gratinDeTopinambour/Reflow_Soldering_DIY/Code_stm32/Drivers/OLED_096/Src/pixel_font.c

/*
 * pixel_font.c
 *
 *  Created on: Oct 25, 2025
 *      Author: valentin
 */

#include "pixel_font.h"

const uint8_t bpixel [] =
{
	// Character: '0'
	0b11000001,
	0b10111010,
	0b10110110,
	0b10101110,
	0b11000001,

	// Character: '1'
	0b11111111,
	0b10111101,
	0b10000000,
	0b10111111,
	0b11111111,

	//Character: 2
	0b10111101,
	0b10011110,
	0b10101110,
	0b10110110,
	0b10111001,

	//Character: 3
	0b11011101,
	0b10111110,
	0b10110110,
	0b10110110,
	0b11001001,

	//Character: 4
	0b11100111,
	0b11101011,
	0b11101101,
	0b11101110,
	0b10000000,

	//Character: 5
	0b10110000,
	0b10110110,
	0b10110110,
	0b10110110,
	0b11001110,

	//Character: 6
	0b11000001,
	0b10110110,
	0b10110110,
	0b10110110,
	0b11001101,

	//Character: 7
	0b11111110,
	0b11111110,
	0b10011110,
	0b11100110,
	0b11111000,

	//Character: 8
	0b11001001,
	0b10110110,
	0b10110110,
	0b10110110,
	0b11001001,

	//Character: 9
	0b10111001,
	0b10110110,
	0b10110110,
	0b10110110,
	0b11000001,

	//Character: A (+10)
	0b10000001,
	0b11110110,
	0b11110110,
	0b11110110,
	0b10000001,

	//Character: B
	0b10000000,
	0b10110110,
	0b10110110,
	0b10110110,
	0b11001001,

	//Character: C
	0b11000001,
	0b10111110,
	0b10111110,
	0b10111110,
	0b11011101,

	//Character: D
	0b10000000,
	0b10111110,
	0b10111110,
	0b10111110,
	0b11000001,

	//Character: E
	0b10000000,
	0b10110110,
	0b10110110,
	0b10111110,
	0b10111110,

	//Character: F
	0b10000000,
	0b11110110,
	0b11110110,
	0b11110110,
	0b11111110,

	//Character: G
	0b11000001,
	0b10111110,
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
	0b11101010,
	0b11011000,

	//character: : (+65)
	0b11111111,
	0b11111111,
	0b11010111,
	0b11111111,
	0b11111111,

	//character: . (+66)
	0b11111111,
	0b11111111,
	0b10111111,
	0b11111111,
	0b11111111,

	//Character: space (+67)
	0b11111111,
	0b11111111,
	0b11111111,
	0b11111111,
	0b11111111,
};
