gratinDeTopinambour/Reflow_Soldering_DIY/Code_stm32/Drivers/THERMISTOR/Src/NTC_thermistor.c

/*
 * NTC_thermistor.c
 *
 *  Created on: 10 févr. 2026
 *      Author: valentin
 */

#include <NTC_thermistor.h>

const int R_serie = 1799; //resistor in serie with thermistor in ohm

//thermistor value in ohm from datasheet
const uint32_t thermistor_ohm_n40_40_LUT [] =
{
		3208260, //-40°C
		3006060,
		2817910,
		2642750,
		2479610,
		2327570,
		2185830,
		2053610,
		1930220,
		1815020,
		1707420,
		1607010,
		1513120,
		1425290,
		1343090,
		1266120,
		1194030,
		1126470,
		1063140,
		1003740,
		948010,
		895470,
		846160,
		799860,
		756370,
		715500,
		677090,
		640960,
		606960,
		574970,
		544860,
		516590,
		489940,
		464820,
		441120,
		418760,
		397660,
		377730,
		358910,
		341130,
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
};

const uint16_t thermistor_ohm_41_230_LUT [] =
{
		51210, //41°C
		49200,
		47280,
		45450,
		43690,
		42010,
		40410,
		38870,
		37390,
		35980,
		34630,
		33340,
		32100,
		30910,
		29780,
		28680,
		27640,
		26630,
		25670,
		24750,
		23860,
		23010,
		22200,
		21410,
		20660,
		19940,
		19240,
		18570,
		17930,
		17320,
		16720,
		16150,
		15600,
		15080,
		14570,
		14080,
		13610,
		13160,
		12720,
		12310,
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
};

const uint8_t thermistor_ohm_231_300_LUT [] =
{
		252, //231°C
		247,
		242,
		237,
		233,
		228,
		224,
		219,
		215,
		211,
		207,
		203,
		199,
		195,
		192,
		188,
		184,
		181,
		178,
		174,
		171,
		168,
		165,
		162,
		159,
		156,
		153,
		150,
		147,
		145,
		142,
		139,
		137,
		134,
		132,
		130,
		127,
		125,
		123,
		121,
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
};


static uint32_t NTC_Rth_Value(uint16_t dig_value)
{
	if(dig_value == 0) return 3208260;
	float Rth = R_serie*(4096.0/((float)dig_value) - 1.0);
	return (uint32_t)Rth;
}

int NTC_Read_Value(ADC_HandleTypeDef *Rth_ADC)
{
	uint16_t adc_value;
	uint32_t Rth_value;
	HAL_ADC_Start(Rth_ADC);
	HAL_ADC_PollForConversion(Rth_ADC, 10);
	adc_value = HAL_ADC_GetValue(Rth_ADC);
	Rth_value = NTC_Rth_Value(adc_value);

	HAL_ADC_Stop(Rth_ADC);

	if(Rth_value < 255)
	{
		for(uint8_t i = 0; i < 70; i++)
		{
			if(Rth_value >= thermistor_ohm_231_300_LUT[i])
			{
				return (int)(i + 231);
			}
		}
		return 300;
	}
	else if(Rth_value < 53310)
	{
		for(uint8_t i = 0; i < 190; i++)
		{
			if(Rth_value >= thermistor_ohm_41_230_LUT[i])
			{
				return (int)(i + 41);
			}
		}
		return 230;
	}
	else
	{
		for(uint8_t i = 0; i < 81; i++)
		{
			if(Rth_value >= thermistor_ohm_n40_40_LUT[i])
			{
				return (int)(i - 40);
			}
		}
		return 40;
	}

}
