gratinDeTopinambour/Reflow_Soldering_DIY/Code_stm32/Drivers/OLED_096/Inc/pixel_font.h

/*
 * pixel_font.h
 *
 *  Created on: Jan 17, 2026
 *      Author: valentin
 */

#ifndef EPAPER_LIB_INC_PIXEL_FONT_H_
#define EPAPER_LIB_INC_PIXEL_FONT_H_

#include <stdint.h>


extern const uint8_t bpixel[];


#endif /* EPAPER_LIB_INC_PIXEL_FONT_H_ */
